Wollivan/SquadronLeader/images/full-set-v2-blue.jpg

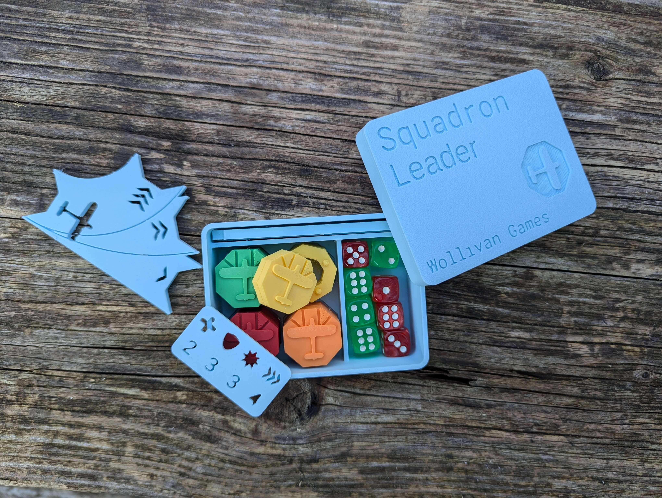
images/full-set-v2-blue.jpg
