Wollivan/SquadronLeader/images/full-set-v2-lined-up-03.jpg

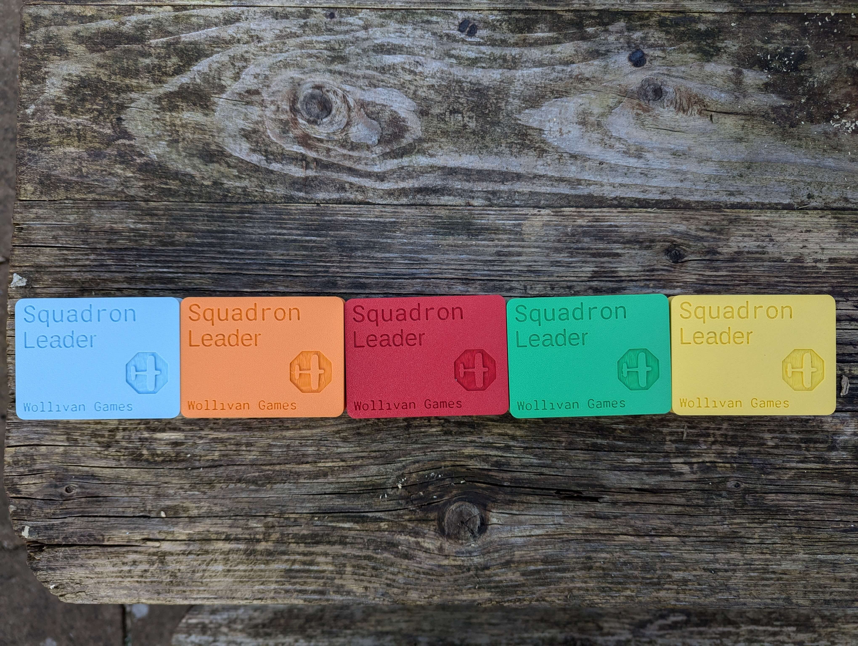
images/full-set-v2-lined-up-03.jpg
