Wollivan/SquadronLeader/images/full-set-v2-orange.jpg

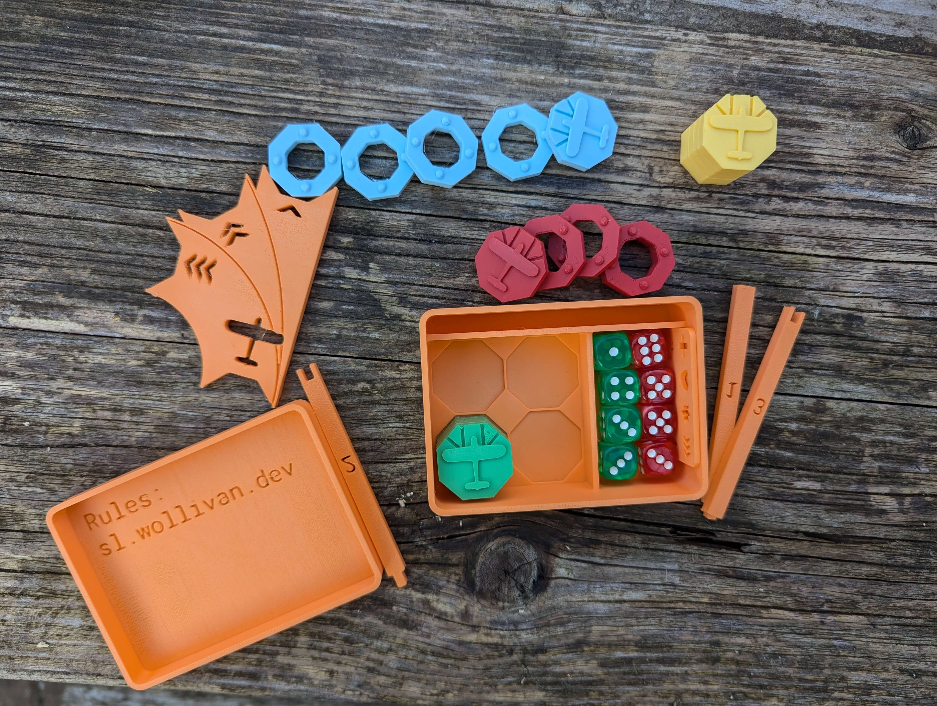
images/full-set-v2-orange.jpg
