Wollivan/SquadronLeader/Rules/ManoeuvreDiagrams/manoeuvres.png

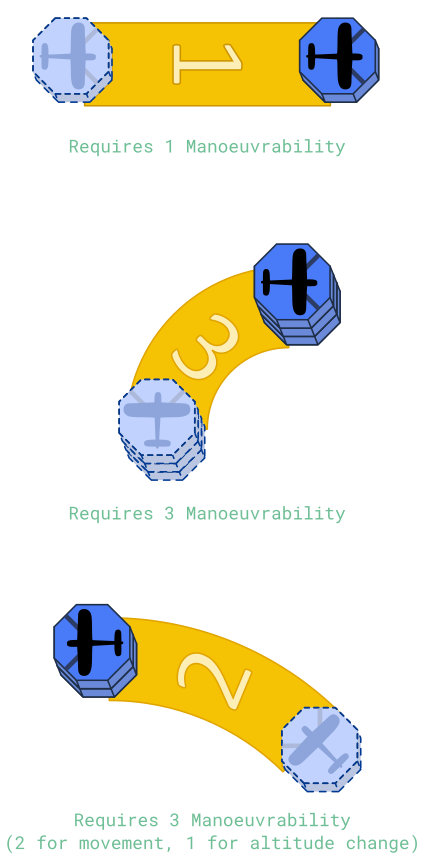
Rules/ManoeuvreDiagrams/manoeuvres.png
