Wollivan/SquadronLeader/Rules/Rulebook/images/qr.png

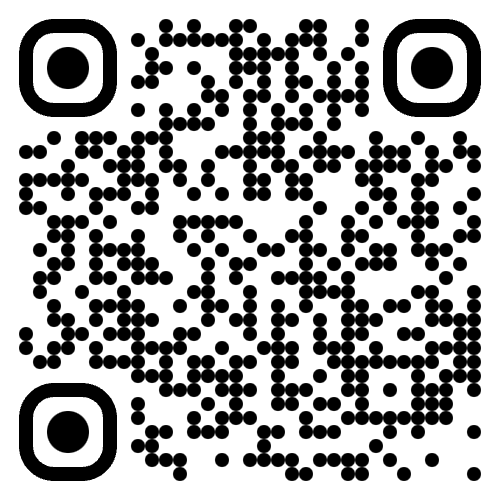
Rules/Rulebook/images/qr.png
