Wollivan/SquadronLeader/Expansions/X-Wing_Compatibility/STLs/plane_xwing_tmg_large.stl

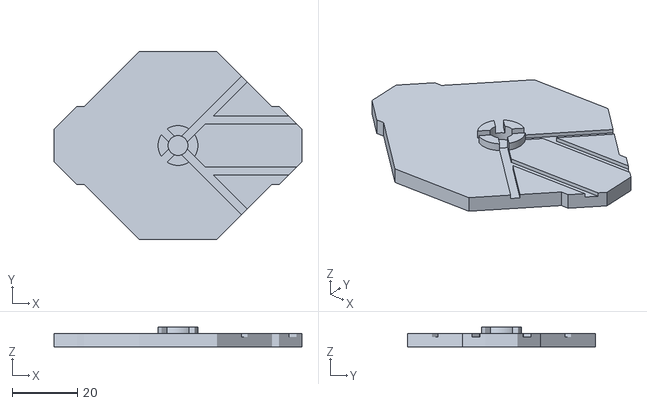
[picture p41: CAD file, 2023-05-31]
Expansions/X-Wing_Compatibility/STLs/plane_xwing_tmg_large.stl
76.0 x 57.7 x 6.00
