Wollivan/SquadronLeader/3DPrinting/STLs/box_small.stl

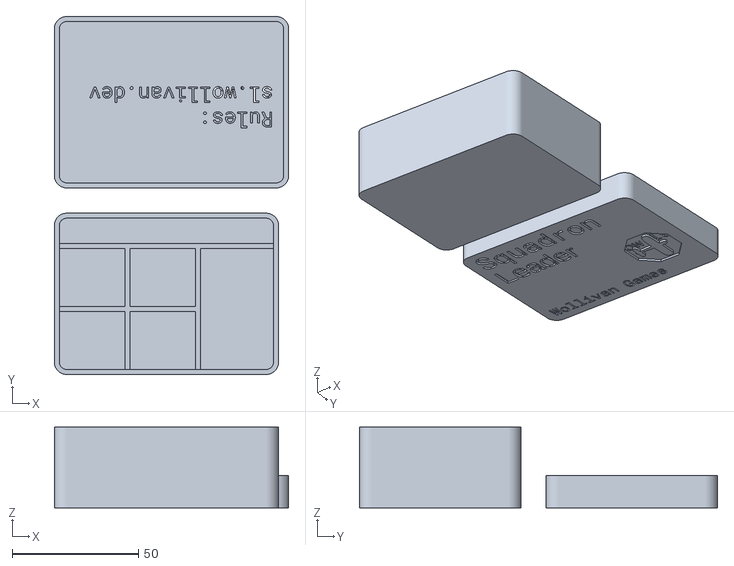
[picture p42: CAD file, 2025-01-22]
3DPrinting/STLs/box_small.stl
93.0 x 142.0 x 32.0
