Wollivan/SquadronLeader/3DPrinting/STLs/individual_models/v1/box.stl

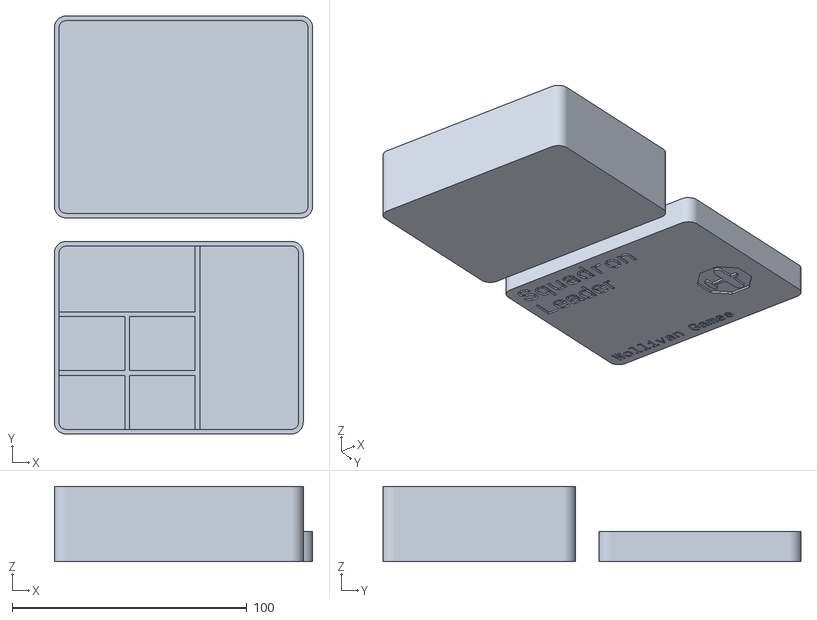
[picture p43: CAD file, 2023-07-18]
3DPrinting/STLs/individual_models/v1/box.stl
110.0 x 178.0 x 32.0
