Wollivan/SquadronLeader/Expansions/Bombers_and_Balloons/STLs/bomb.stl

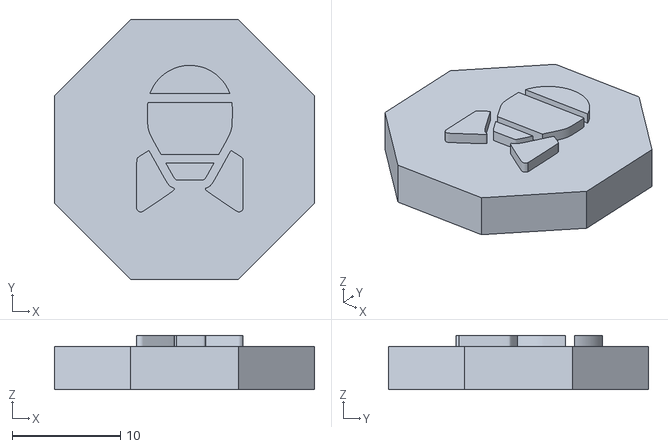
[picture p44: CAD file, 2023-05-25]
Expansions/Bombers_and_Balloons/STLs/bomb.stl
24.0 x 24.0 x 5.00
