Wollivan/SquadronLeader/3DPrinting/STLs/individual_models/range_ruler_3_only.stl

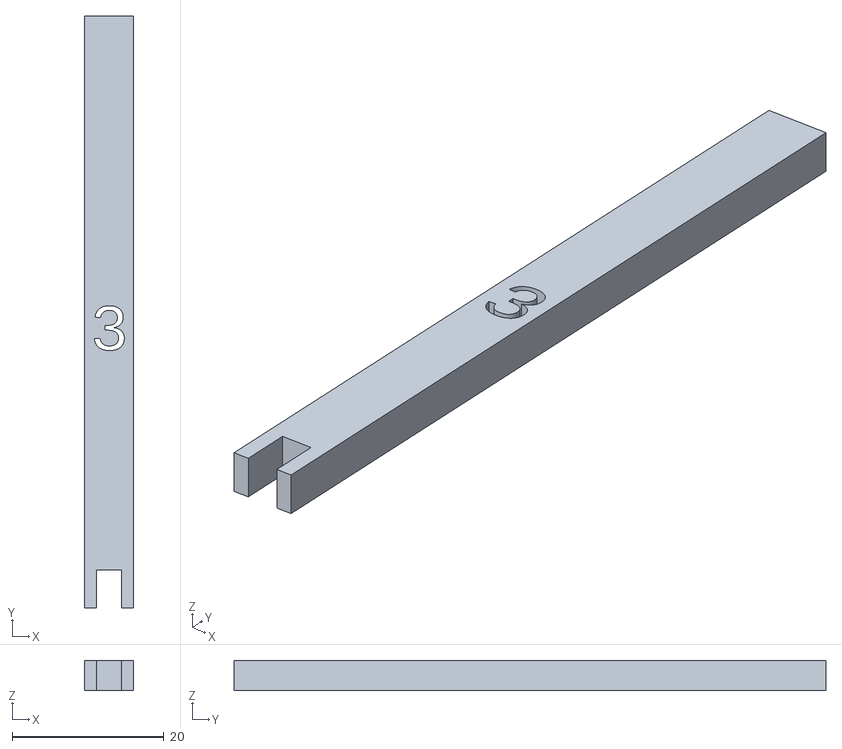
[picture p45: CAD file, 2023-05-10]
3DPrinting/STLs/individual_models/range_ruler_3_only.stl
6.50 x 78.0 x 4.00
