Wollivan/SquadronLeader/3DPrinting/STLs/individual_models/v1/box_base.stl

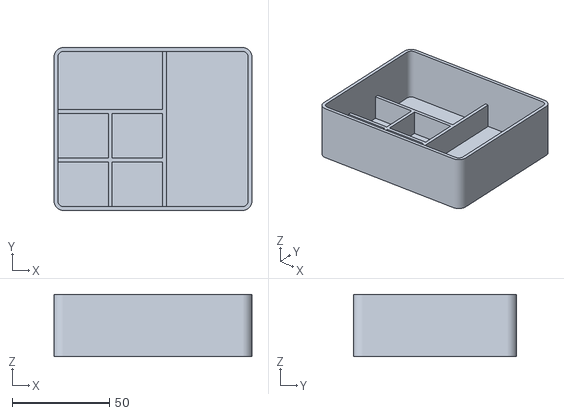
[picture p46: CAD file, 2023-07-18]
3DPrinting/STLs/individual_models/v1/box_base.stl
102.0 x 84.0 x 32.0
