Wollivan/SquadronLeader/3DPrinting/STLs/stat_side.stl

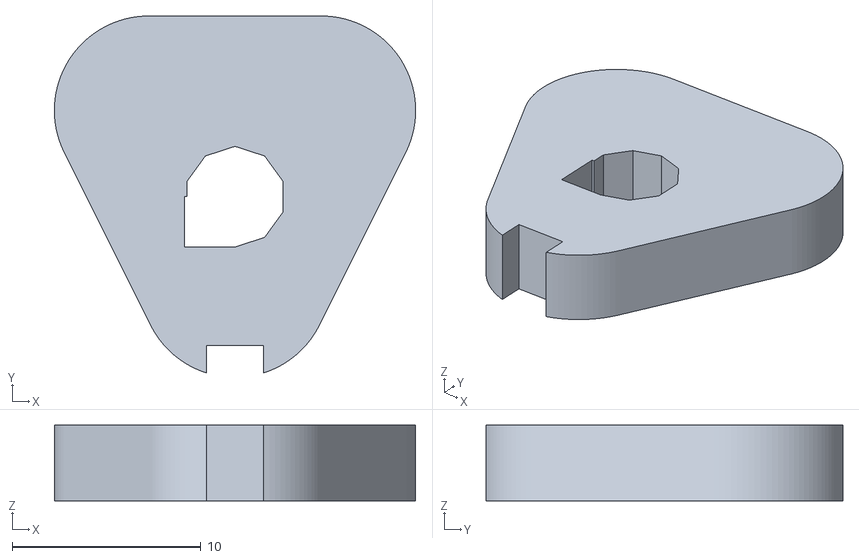
[picture p47: CAD file, 2023-07-18]
3DPrinting/STLs/stat_side.stl
19.1 x 18.9 x 4.00
