Wollivan/SquadronLeader/STLs/statwheel_outer_axle.stl

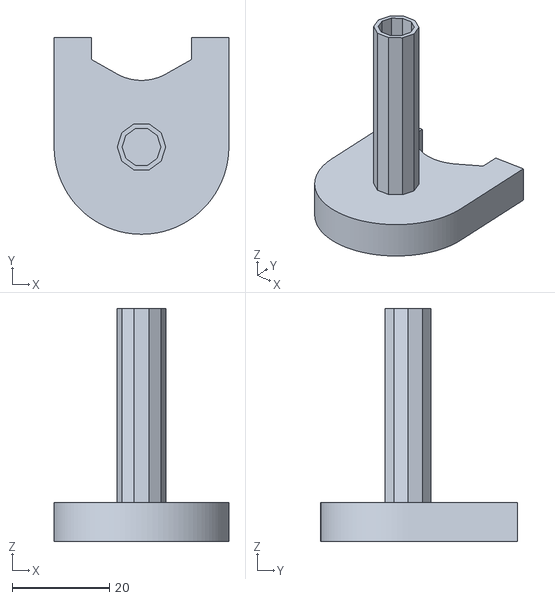
[picture p48: CAD file, 2024-04-24]
STLs/statwheel_outer_axle.stl
36.0 x 40.5 x 48.0
