Wollivan/SquadronLeader/3DPrinting/STLs/individual_models/v1/stat_side_two.stl

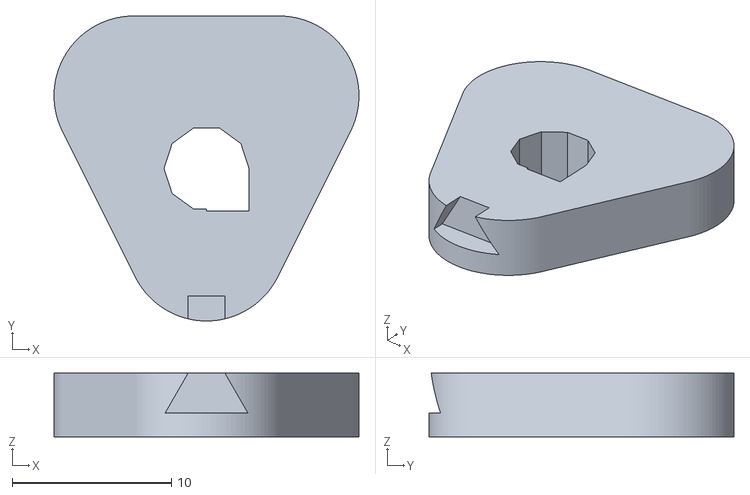
[picture p50: CAD file, 2023-06-25]
3DPrinting/STLs/individual_models/v1/stat_side_two.stl
19.1 x 19.1 x 4.00
