Wollivan/SquadronLeader/3DPrinting/STLs/stat_axel.stl

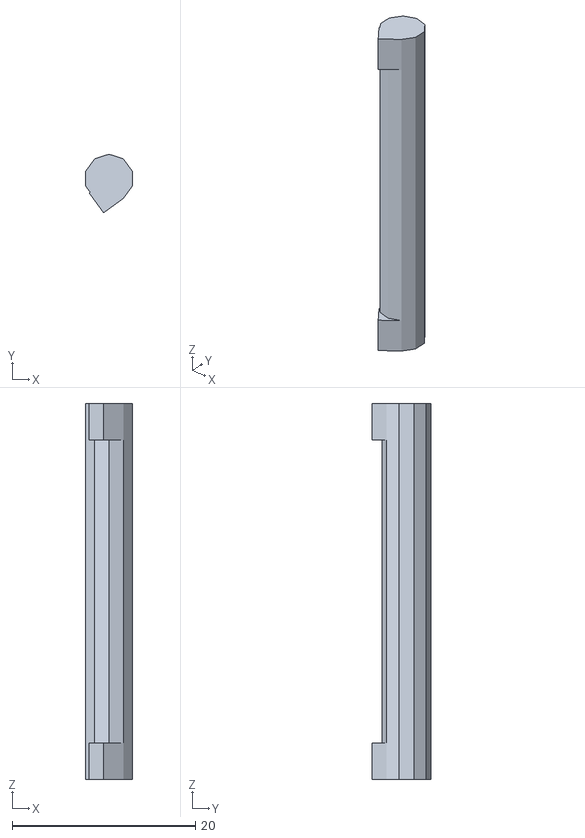
[picture p51: CAD file, 2023-06-15]
3DPrinting/STLs/stat_axel.stl
5.07 x 6.39 x 41.0
