Wollivan/SquadronLeader/STLs/statwheel_inner_axle.stl

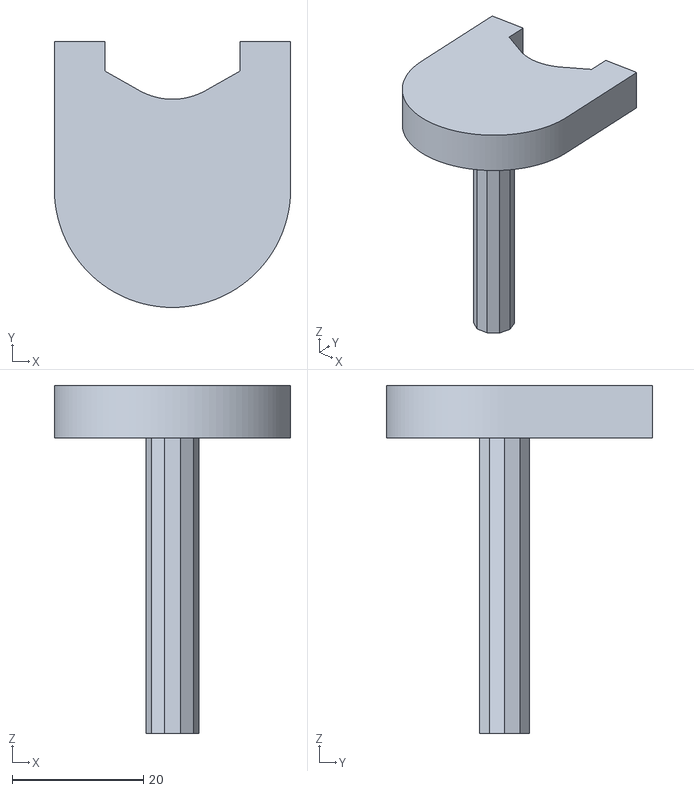
[picture p52: CAD file, 2024-04-24]
STLs/statwheel_inner_axle.stl
36.0 x 40.5 x 53.0
