Wollivan/SquadronLeader/3DPrinting/STLs/individual_models/range_ruler_1_only.stl

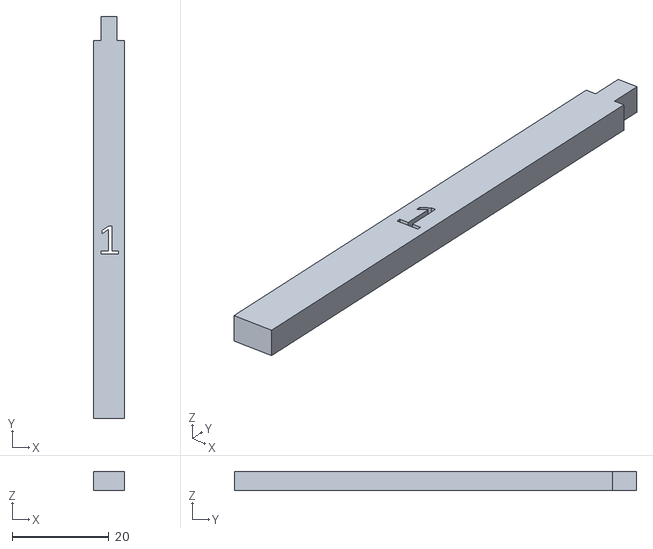
[picture p53: CAD file, 2023-05-10]
3DPrinting/STLs/individual_models/range_ruler_1_only.stl
6.50 x 83.0 x 4.00
