Wollivan/SquadronLeader/3DPrinting/STLs/range_ruler.stl

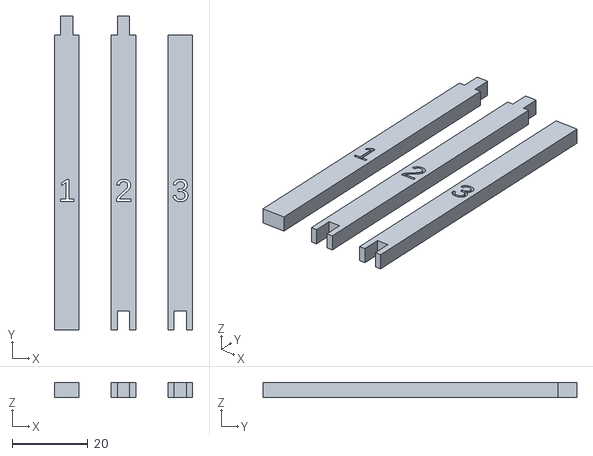
[picture p54: CAD file, 2023-05-10]
3DPrinting/STLs/range_ruler.stl
36.5 x 83.0 x 4.00
