Wollivan/SquadronLeader/3DPrinting/STLs/individual_models/maneuver_turn.stl

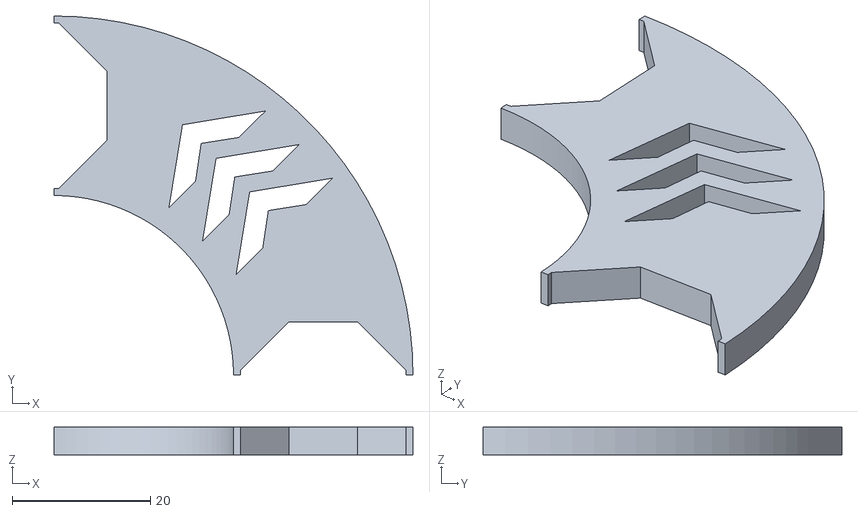
[picture p55: CAD file, 2023-01-25]
3DPrinting/STLs/individual_models/maneuver_turn.stl
52.0 x 52.0 x 4.00
