Wollivan/SquadronLeader/3DPrinting/STLs/individual_models/v1/stat_wheel_attack.stl

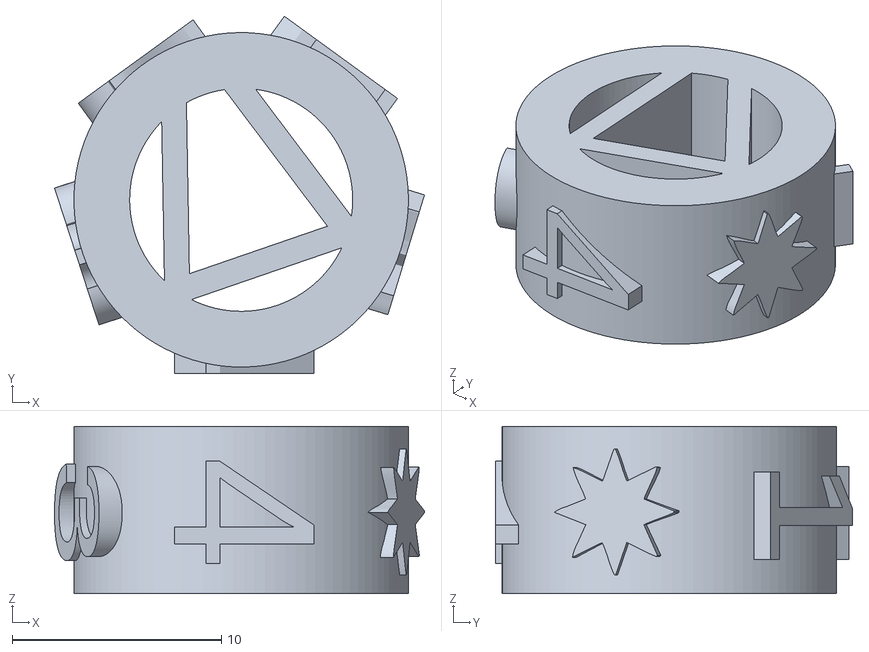
[picture p56: CAD file, 2023-06-25]
3DPrinting/STLs/individual_models/v1/stat_wheel_attack.stl
17.7 x 17.1 x 8.00
