Wollivan/SquadronLeader/3DPrinting/STLs/manoeuvre_template.stl

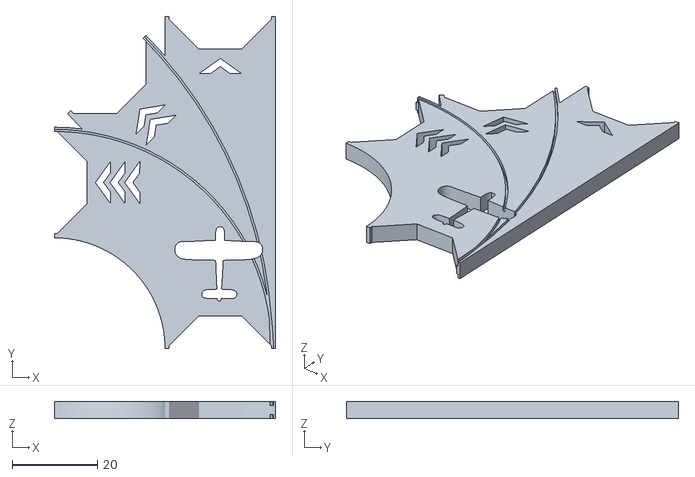
[picture p57: CAD file, 2023-01-06]
3DPrinting/STLs/manoeuvre_template.stl
52.0 x 78.0 x 4.00
