Wollivan/SquadronLeader/STLs/player_plane_blank.stl

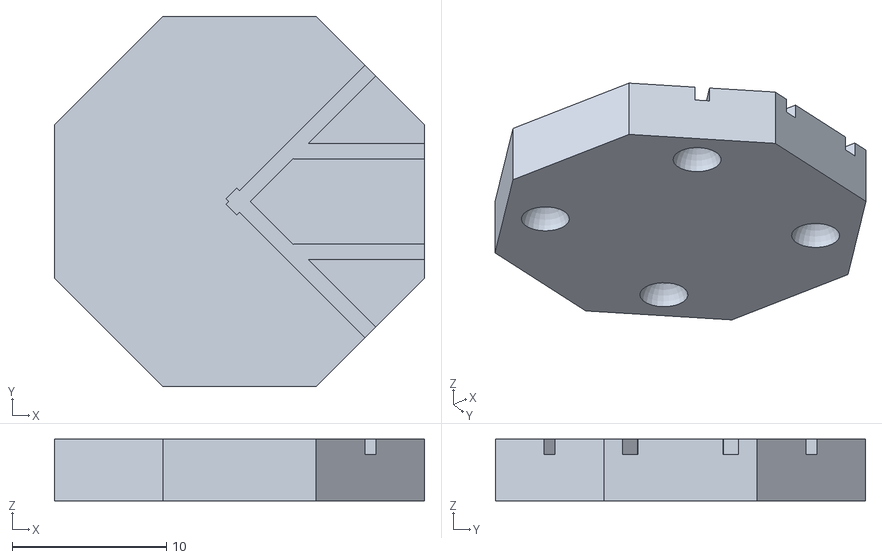
[picture p58: CAD file, 2022-04-21]
STLs/player_plane_blank.stl
24.0 x 24.0 x 4.00
