Wollivan/SquadronLeader/3DPrinting/STLs/individual_models/maneuver_bank.stl

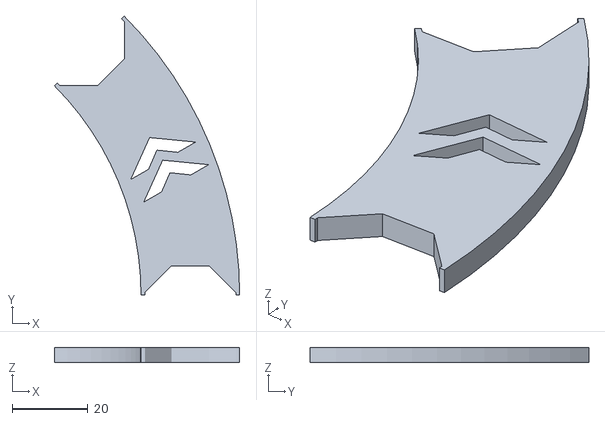
[picture p59: CAD file, 2023-01-25]
3DPrinting/STLs/individual_models/maneuver_bank.stl
48.8 x 73.5 x 4.00
