Wollivan/SquadronLeader/3DPrinting/STLs/individual_models/v1/box_wo_insert_small.stl

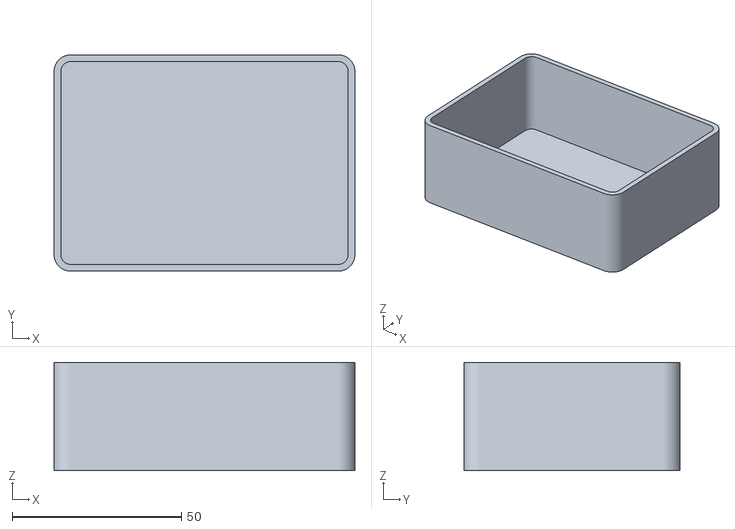
[picture p60: CAD file, 2023-06-25]
3DPrinting/STLs/individual_models/v1/box_wo_insert_small.stl
89.0 x 64.0 x 32.0
