Wollivan/SquadronLeader/3DPrinting/STLs/player.stl

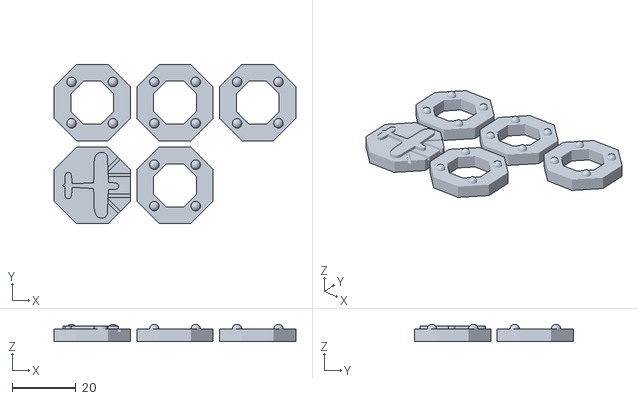
[picture p61: CAD file, 2022-12-31]
3DPrinting/STLs/player.stl
76.0 x 50.0 x 5.49
