Wollivan/SquadronLeader/STLs/move_straight.stl

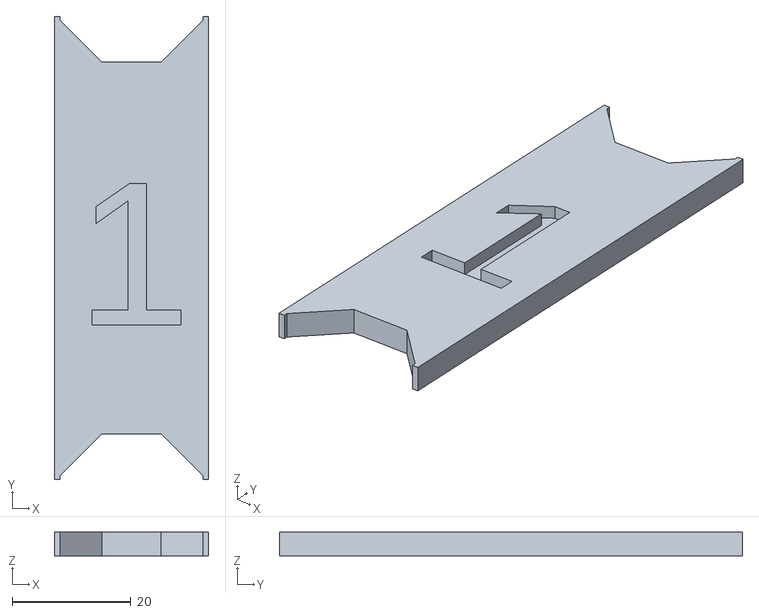
[picture p62: CAD file, 2022-04-21]
STLs/move_straight.stl
26.0 x 78.0 x 4.00
