Wollivan/SquadronLeader/3DPrinting/STLs/individual_models/maneuver_straight.stl

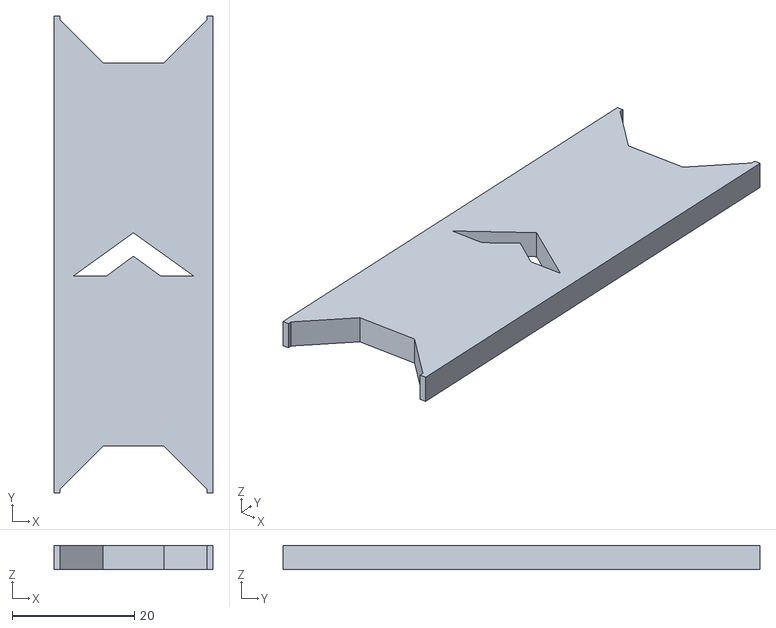
[picture p63: CAD file, 2023-01-25]
3DPrinting/STLs/individual_models/maneuver_straight.stl
26.0 x 78.0 x 4.00
