Wollivan/SquadronLeader/STLs/move_bank.stl

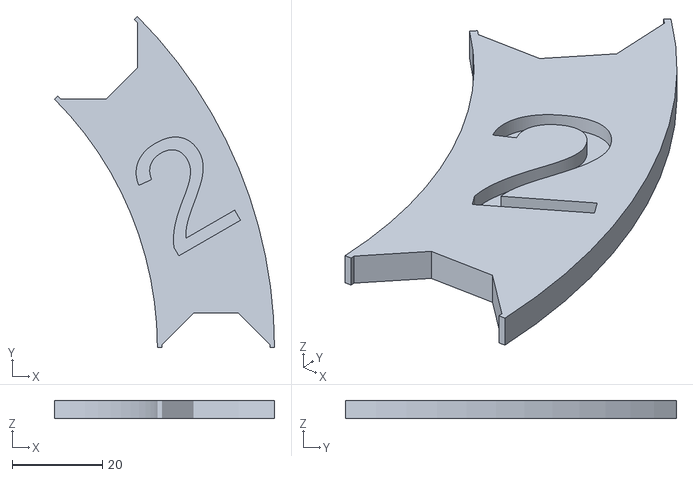
[picture p64: CAD file, 2022-04-21]
STLs/move_bank.stl
48.8 x 73.5 x 4.00
