Wollivan/SquadronLeader/3DPrinting/STLs/individual_models/range_ruler_single.stl

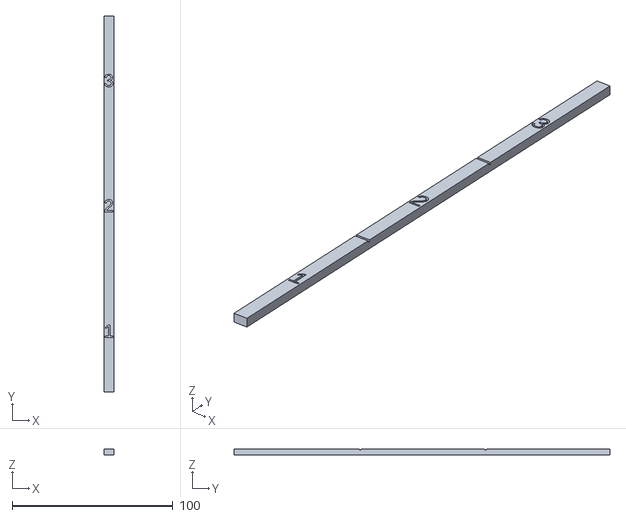
[picture p65: CAD file, 2022-05-15]
3DPrinting/STLs/individual_models/range_ruler_single.stl
6.50 x 234.0 x 4.00
