Wollivan/SquadronLeader/3DPrinting/STLs/individual_models/player_altitude.stl

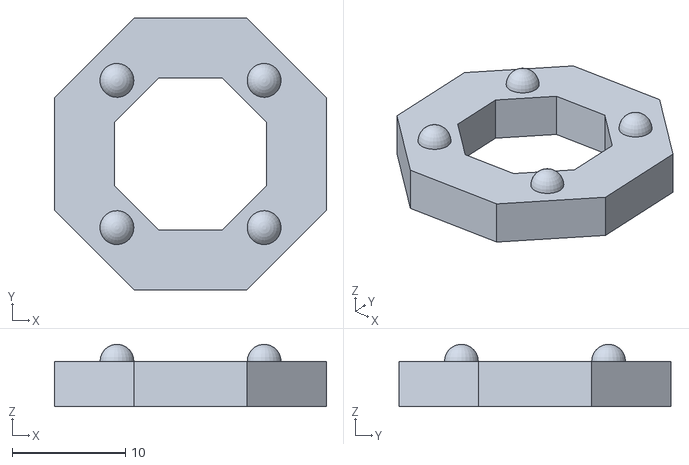
[picture p67: CAD file, 2022-05-06]
3DPrinting/STLs/individual_models/player_altitude.stl
24.0 x 24.0 x 5.49
