Wollivan/SquadronLeader/3DPrinting/STLs/individual_models/v1/box_wo_insert.stl

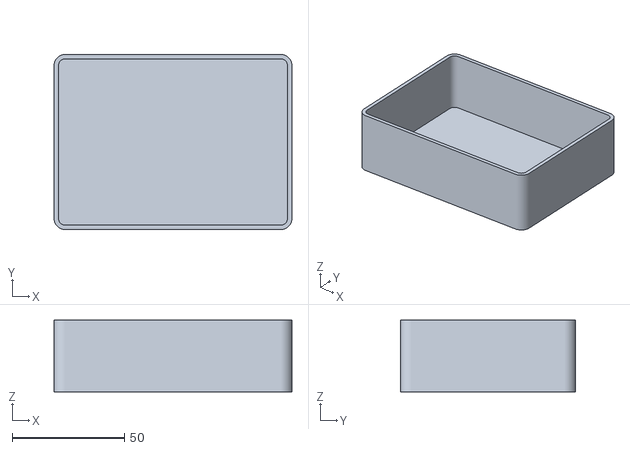
[picture p68: CAD file, 2023-06-24]
3DPrinting/STLs/individual_models/v1/box_wo_insert.stl
106.0 x 78.0 x 32.0
