Wollivan/SquadronLeader/3DPrinting/STLs/individual_models/v1/stat_board.stl

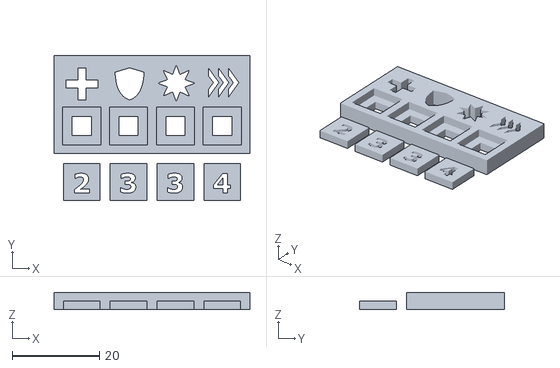
[picture p69: CAD file, 2023-06-03]
3DPrinting/STLs/individual_models/v1/stat_board.stl
45.0 x 33.2 x 4.00
