Wollivan/SquadronLeader/3DPrinting/STLs/individual_models/v1/stats_board_only.stl

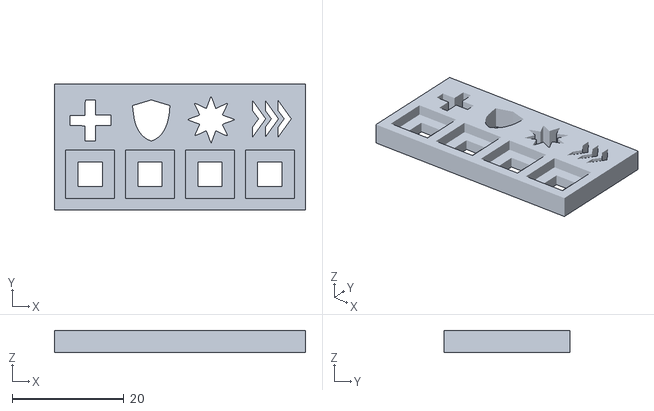
[picture p70: CAD file, 2023-06-03]
3DPrinting/STLs/individual_models/v1/stats_board_only.stl
45.0 x 22.5 x 4.00
