Wollivan/SquadronLeader/3DPrinting/STLs/individual_models/v1/stats_chits_only.stl

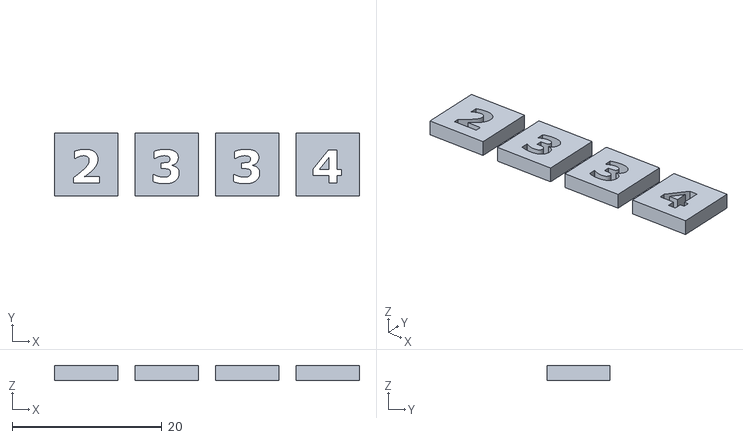
[picture p71: CAD file, 2023-06-03]
3DPrinting/STLs/individual_models/v1/stats_chits_only.stl
40.7 x 8.45 x 2.00
