Wollivan/SquadronLeader/3DPrinting/OpenSCAD/bombers_and_balloons.scad

// bomb icon - <a href="https://www.flaticon.com/free-icons/atomic-bomb" title="atomic bomb icons">Atomic bomb icons created by Freepik - Flaticon</a>
// balloon icon - <a href="https://www.flaticon.com/free-icons/hot-air-balloon" title="hot air balloon icons">Hot air balloon icons created by Freepik - Flaticon</a>
include <variables.scad>;
include <modules.scad>;


module bomber() {
    largePlane();
}
module bombIcon() {
    translate([0.5,1,tokenHeight])
        linear_extrude(height = tokenHeight/4) {
            scale(0.075)
                import("icons/bomb.svg", center=true);
    }
}

module bomb() {
    union(){
        token();

        bombIcon();
    }
}

module balloonIcon() {
    translate([0.5,1,tokenHeight])
        linear_extrude(height = tokenHeight/4) {
            scale(0.1)
                import("icons/balloon.svg", center=true);
    }
}

module balloon() {
    scale([2,2,1])
        union(){
            token();

            balloonIcon();
        }
}

bomber();
translate([0,tokenWidth*2,0]) bomb();
translate([0,tokenWidth*4,0]) rotate([0,0,90]) balloon();
