Wollivan/SquadronLeader/3DPrinting/OpenSCAD/variables.scad

tokenHeight = 4;
tokenWidth = 26;
wallWidth = 6;
$fn = 100;

arcWidth = 1;

templateGapOffset = tokenWidth/6;
templateLength = tokenWidth*3;

//stat board variables
statHeight=1.8;
numberHeight=statHeight/2.5;
boardWidth=tokenWidth;
boardHeight=tokenWidth*1.5;
tokenSpace=2.27;//this could be calculated
tokenRad=5;//7.32;
tokenRadSm=tokenRad*.924;
pegSpace=6;
pegHoleRad=1.6;
